Brunoarico/LIDARO/imagens/chao.png

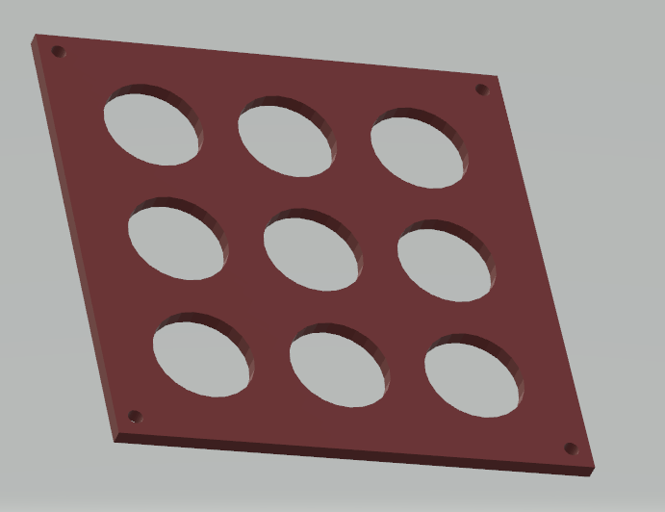
imagens/chao.png
