Brunoarico/LIDARO/imagens/coluna.png

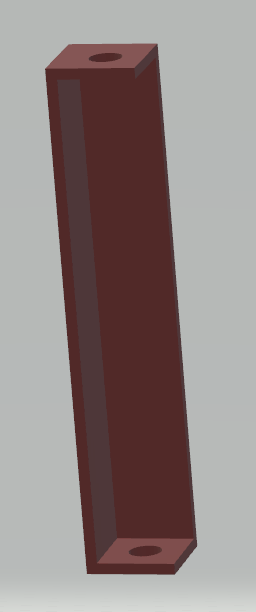
imagens/coluna.png
