Brunoarico/LIDARO/imagens/Lidar1.png

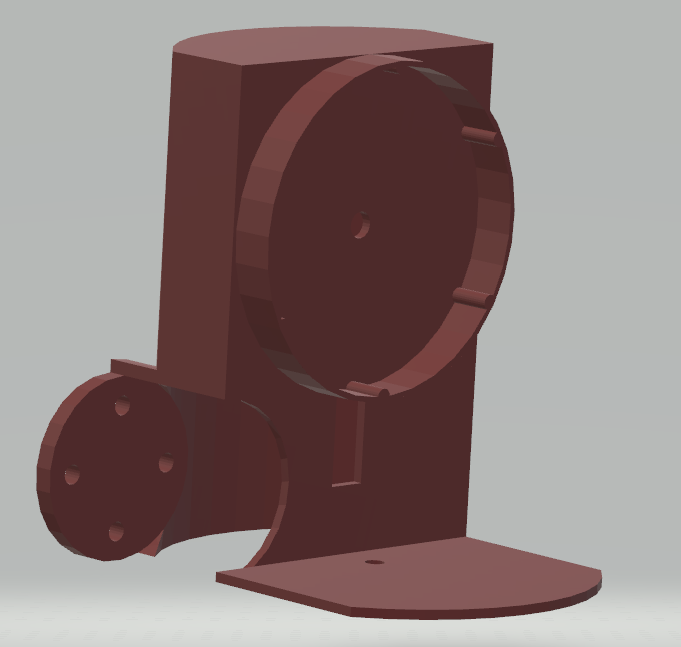
imagens/Lidar1.png
