Brunoarico/LIDARO/imagens/montado4.png

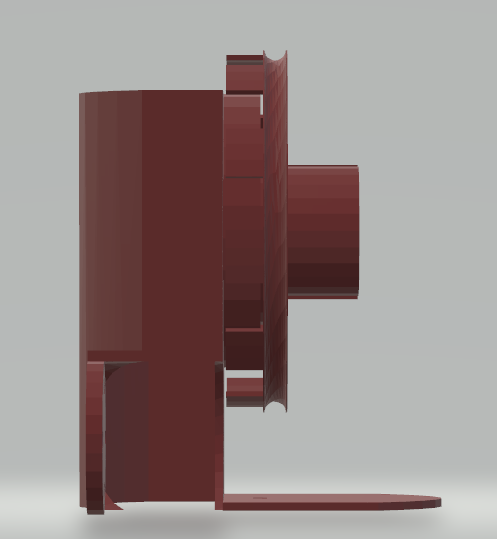
imagens/montado4.png
