Brunoarico/LIDARO/imagens/montado.png

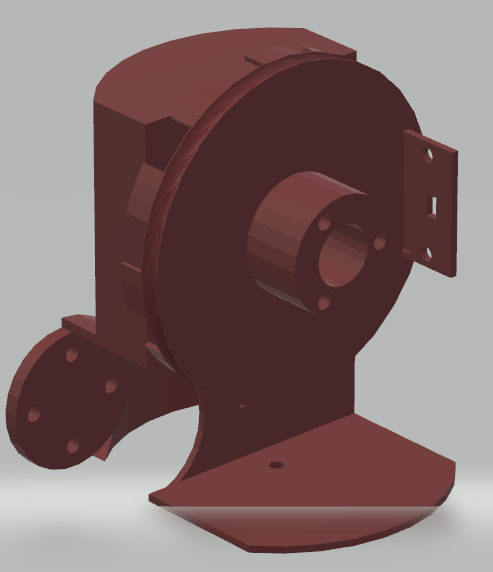
imagens/montado.png
