Brunoarico/LIDARO/imagens/PCB.png

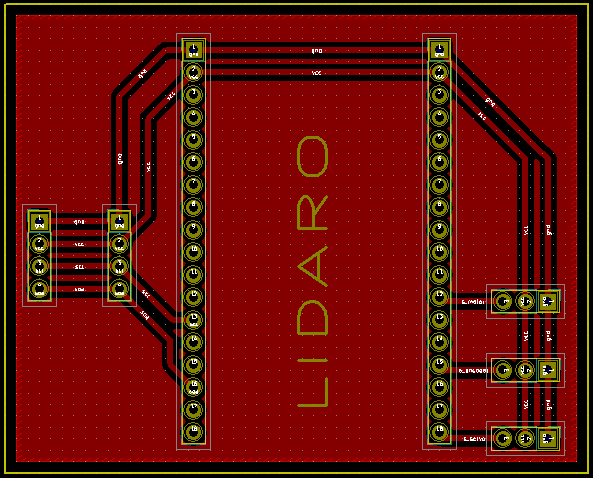
imagens/PCB.png
