Brunoarico/LIDARO/imagens/Rotor1.png

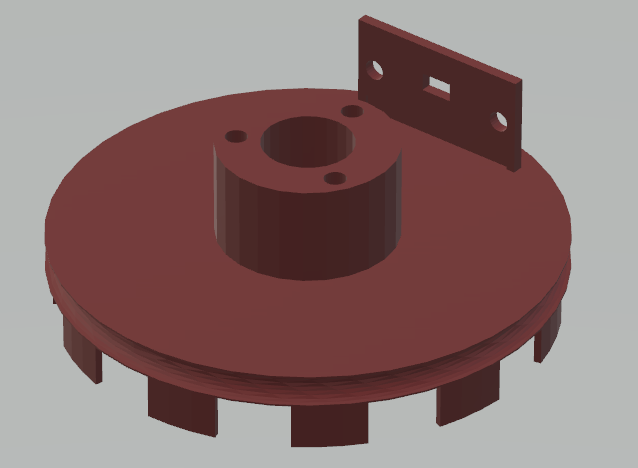
imagens/Rotor1.png
