Brunoarico/LIDARO/imagens/rotor2.png

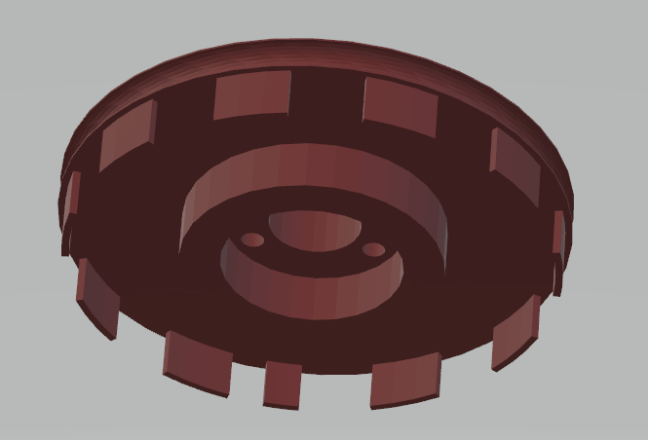
imagens/rotor2.png
