Brunoarico/LIDARO/imagens/sch.png

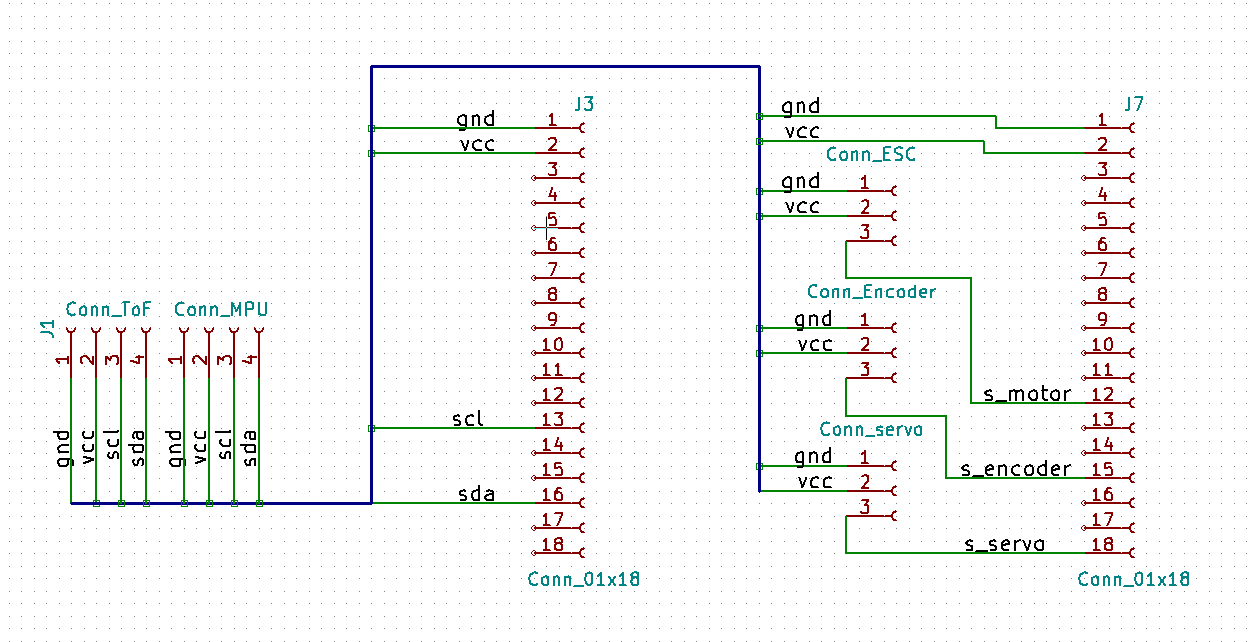
imagens/sch.png
