Brunoarico/LIDARO/imagens/teto.png

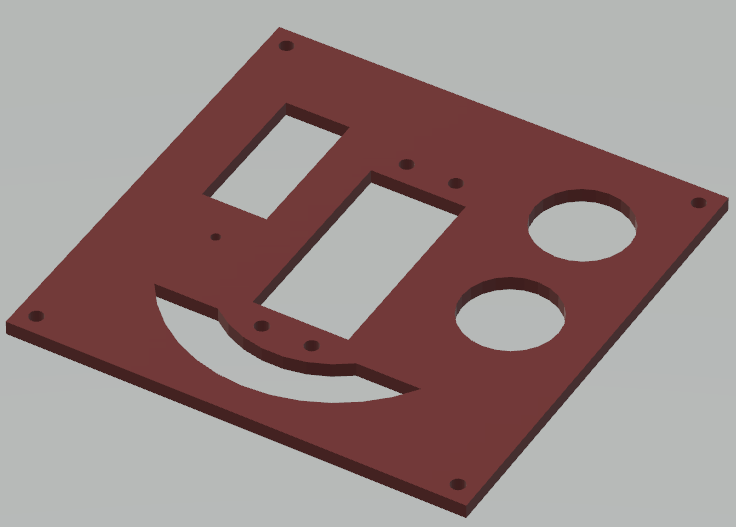
imagens/teto.png
